stop-pattern/SpeedometerDriveBoard/code/firm/declarate.cpp

/*----------variants---------*/
//needle
double Speed;
double ORP;

//lamp
int indicator[25];
int R, G, notice, P, X, BL;
bool bell;// = false;
int L15, L60, ATS;

//system
int cnt;
bool shiftregister[50]; //シフトレジスタ送信値
long int  reg;

bool isSW;
