stop-pattern/SpeedometerDriveBoard/code/board_test/BIDSino/BIDSino.ino

<<<<<<< HEAD
/* BIDS_SerConとArduinoでシリアル通信させるサンプルプスケッチ
   エラー情報を無視するバージョン
   詳細は同封の説明書をご覧ください。
   License : The MIT License
   Copyright 2018 Tetsu Otter
   Permission is hereby granted, free of charge, to any person obtaining a copy of this software and associated documentation files (the "Software"), to deal in the Software without restriction, including without limitation the rights to use, copy, modify, merge, publish, distribute, sublicense, and/or sell copies of the Software, and to permit persons to whom the Software is furnished to do so, subject to the following conditions:
   The above copyright notice and this permission notice shall be included in all copies or substantial portions of the Software.
   THE SOFTWARE IS PROVIDED "AS IS", WITHOUT WARRANTY OF ANY KIND, EXPRESS OR IMPLIED, INCLUDING BUT NOT LIMITED TO THE WARRANTIES OF MERCHANTABILITY, FITNESS FOR A PARTICULAR PURPOSE AND NONINFRINGEMENT. IN NO EVENT SHALL THE AUTHORS OR COPYRIGHT HOLDERS BE LIABLE FOR ANY CLAIM, DAMAGES OR OTHER LIABILITY, WHETHER IN AN ACTION OF CONTRACT, TORT OR OTHERWISE, ARISING FROM, OUT OF OR IN CONNECTION WITH THE SOFTWARE OR THE USE OR OTHER DEALINGS IN THE SOFTWARE.
*/
#include "define.h"
#include "BIDS.h"

int VersionNum = 100;

void setup() {
  pinMode(LED, OUTPUT);
  digitalWrite(LED, HIGH);
  Serial.begin(115200);
  while (!Serial);
  VersionNum = BIDS::VersionCheck(VersionNum);
}

void loop() {

  if (BIDS::DataGet("I", "D", 0) == 1) {
    digitalWrite(LED, LOW);
  } else {
    digitalWrite(LED, HIGH);
  }

  delay(1);
}
=======
/* BIDS_SerConとArduinoでシリアル通信させるサンプルプスケッチ
   エラー情報を無視するバージョン
   詳細は同封の説明書をご覧ください。
   License : The MIT License
   Copyright 2018 Tetsu Otter
   Permission is hereby granted, free of charge, to any person obtaining a copy of this software and associated documentation files (the "Software"), to deal in the Software without restriction, including without limitation the rights to use, copy, modify, merge, publish, distribute, sublicense, and/or sell copies of the Software, and to permit persons to whom the Software is furnished to do so, subject to the following conditions:
   The above copyright notice and this permission notice shall be included in all copies or substantial portions of the Software.
   THE SOFTWARE IS PROVIDED "AS IS", WITHOUT WARRANTY OF ANY KIND, EXPRESS OR IMPLIED, INCLUDING BUT NOT LIMITED TO THE WARRANTIES OF MERCHANTABILITY, FITNESS FOR A PARTICULAR PURPOSE AND NONINFRINGEMENT. IN NO EVENT SHALL THE AUTHORS OR COPYRIGHT HOLDERS BE LIABLE FOR ANY CLAIM, DAMAGES OR OTHER LIABILITY, WHETHER IN AN ACTION OF CONTRACT, TORT OR OTHERWISE, ARISING FROM, OUT OF OR IN CONNECTION WITH THE SOFTWARE OR THE USE OR OTHER DEALINGS IN THE SOFTWARE.
*/
#include "define.h"
#include "BIDS.h"

int VersionNum = 100;

void setup() {
  pinMode(LED, OUTPUT);
  digitalWrite(LED, HIGH);
  Serial.begin(115200);
  while (!Serial);
  VersionNum = BIDS::VersionCheck(VersionNum);
}

void loop() {

  if (BIDS::DataGet("I", "D", 0) == 1) {
    digitalWrite(LED, LOW);
  } else {
    digitalWrite(LED, HIGH);
  }

  delay(1);
}
>>>>>>> acf3d5ac075861e1d6ade95787c2d3ec12d00e4b
