stop-pattern/SpeedometerDriveBoard/code/board_test/BIDSino/BIDS.cpp

<<<<<<< HEAD
#include <arduino.h>
#include "BIDS.h"

float BIDS::SerialGet(String Command) {
  Serial.print(Command);
  Serial.print("\n");
  //Serial.println();
  while (Serial.available() <= 0);
  String GetData = Serial.readStringUntil('\n');
  GetData.replace("\n", "");
  if (GetData.startsWith(Command)) {
    GetData.replace(Command + "X", "");
    return GetData.toFloat();
  }
  return 0;
}

float BIDS::DataGet(String Identifier, String Symbol, int Num) {
  return SerialGet("TR" + Identifier + Symbol + String(Num));
}
float BIDS::DataGet(String Identifier, int Num) {
  return DataGet(Identifier, "", Num);
}

int BIDS::VersionCheck(int VersionNum) {
  int ret;
  int vnum = DataGet("V", VersionNum);
  ret = vnum < VersionNum ? VersionNum : vnum;
  return ret;
}
=======
#include <arduino.h>
#include "BIDS.h"

float BIDS::SerialGet(String Command) {
  Serial.print(Command);
  Serial.print("\n");
  //Serial.println();
  while (Serial.available() <= 0);
  String GetData = Serial.readStringUntil('\n');
  GetData.replace("\n", "");
  if (GetData.startsWith(Command)) {
    GetData.replace(Command + "X", "");
    return GetData.toFloat();
  }
  return 0;
}

float BIDS::DataGet(String Identifier, String Symbol, int Num) {
  return SerialGet("TR" + Identifier + Symbol + String(Num));
}
float BIDS::DataGet(String Identifier, int Num) {
  return DataGet(Identifier, "", Num);
}

int BIDS::VersionCheck(int VersionNum) {
  int ret;
  int vnum = DataGet("V", VersionNum);
  ret = vnum < VersionNum ? VersionNum : vnum;
  return ret;
}
>>>>>>> acf3d5ac075861e1d6ade95787c2d3ec12d00e4b
