stop-pattern/SpeedometerDriveBoard/code/board_test/BIDSino/BIDS.h

<<<<<<< HEAD
namespace BIDS {
float SerialGet(String);
float DataGet(String, String, int);
float DataGet(String, int);
int VersionCheck(int);
};
=======
namespace BIDS {
float SerialGet(String);
float DataGet(String, String, int);
float DataGet(String, int);
int VersionCheck(int);
};
>>>>>>> acf3d5ac075861e1d6ade95787c2d3ec12d00e4b
