stop-pattern/SpeedometerDriveBoard/code/board_test/shiftregister/declarate.cpp

<<<<<<< HEAD
/*----------variants---------*/
bool shiftregister[50]; //シフトレジスタ送信値
long int  reg;
=======
/*----------variants---------*/
bool shiftregister[50]; //シフトレジスタ送信値
long int  reg;
>>>>>>> acf3d5ac075861e1d6ade95787c2d3ec12d00e4b
